Workshopshed/EnchantedObjects/Code/Examples/Blinker/123DDemo.png

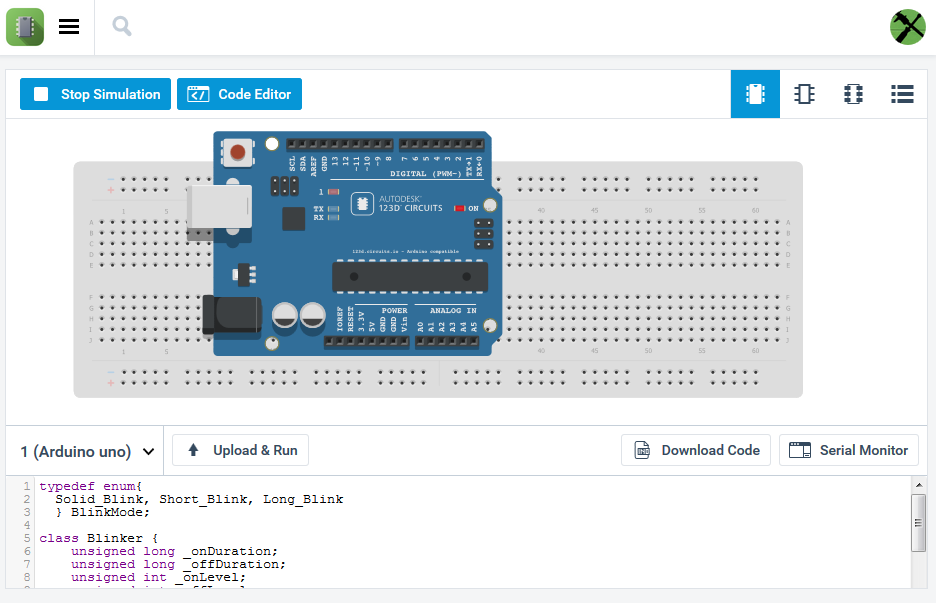
Code/Examples/Blinker/123DDemo.png
