Workshopshed/EnchantedObjects/Code/Examples/HandshakingMonitor/BootOff.jpg

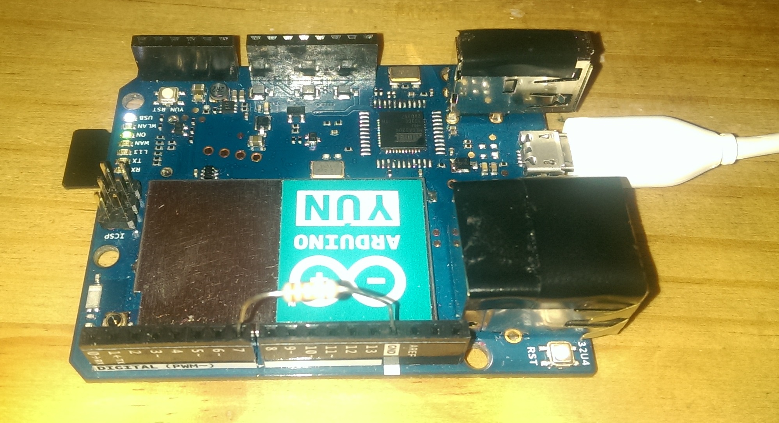
Code/Examples/HandshakingMonitor/BootOff.jpg
