Workshopshed/EnchantedObjects/Code/Examples/HandshakingMonitor/BootOn.jpg

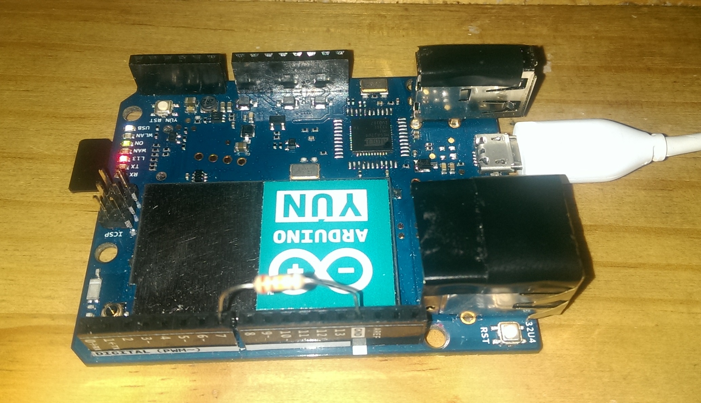
Code/Examples/HandshakingMonitor/BootOn.jpg
