Workshopshed/EnchantedObjects/Code/Examples/HandshakingMonitor/Shell.png

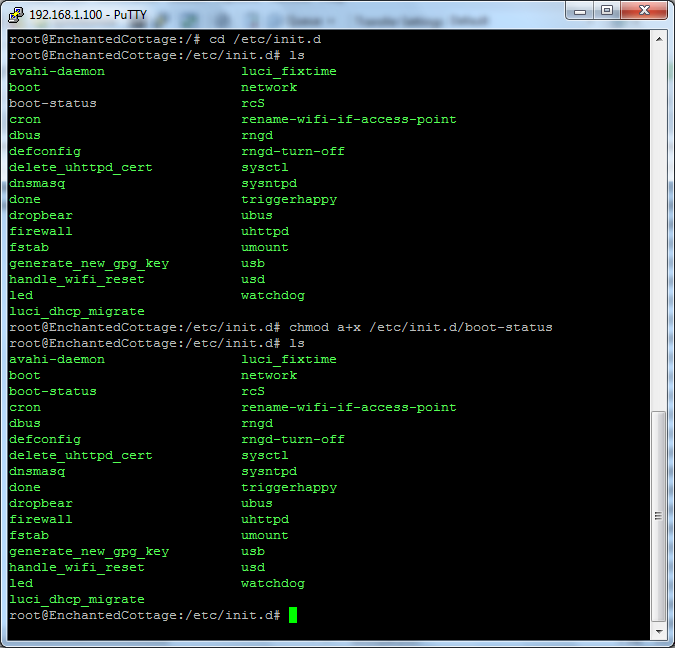
Code/Examples/HandshakingMonitor/Shell.png
