Workshopshed/EnchantedObjects/Code/Examples/LibraryManager.png

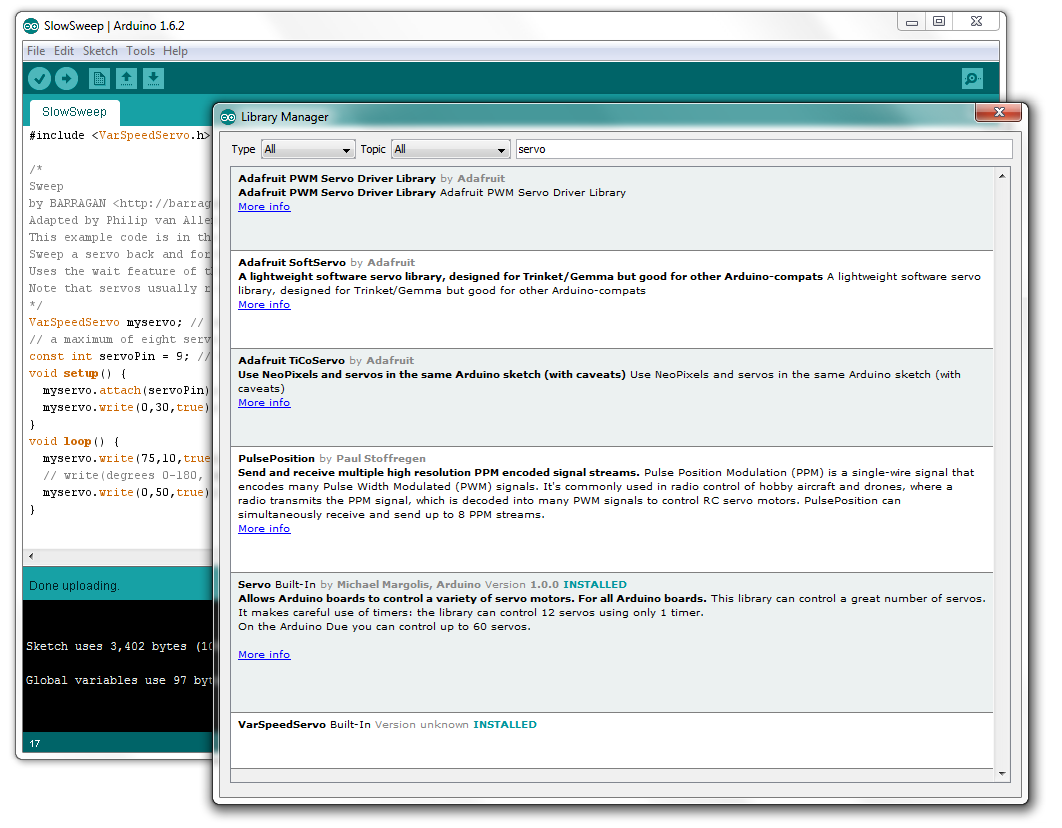
Code/Examples/LibraryManager.png
