Workshopshed/EnchantedObjects/Code/Examples/Python/PythonHello.png

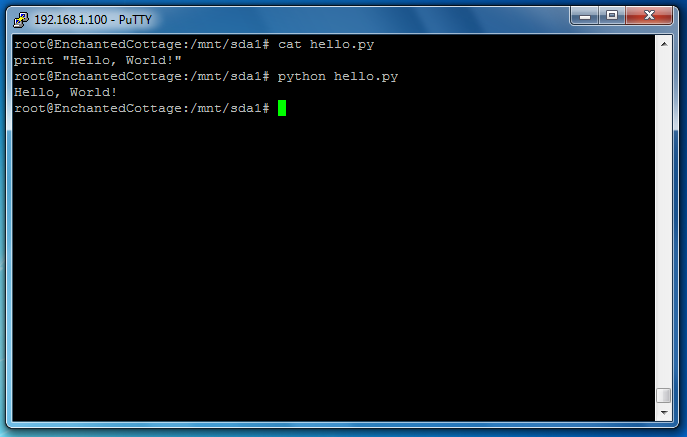
Code/Examples/Python/PythonHello.png
