Workshopshed/EnchantedObjects/Code/Examples/Python/PythonIDE.png

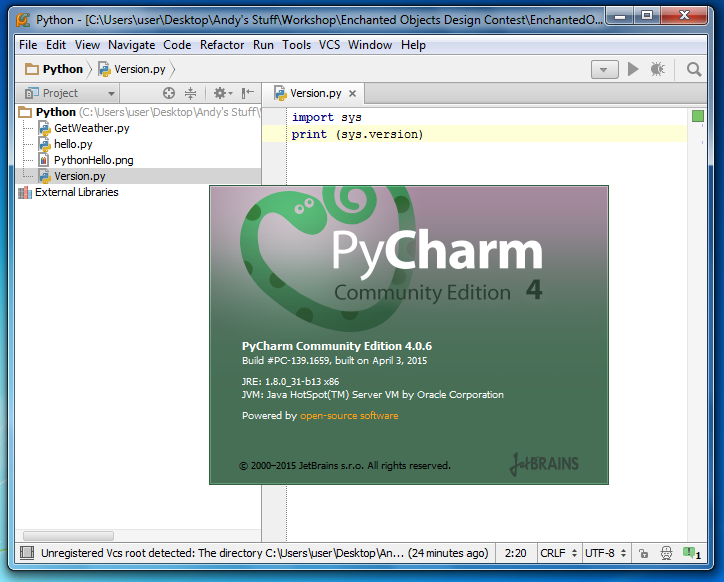
Code/Examples/Python/PythonIDE.png
