Workshopshed/EnchantedObjects/Code/Examples/Python/SourceSync.png

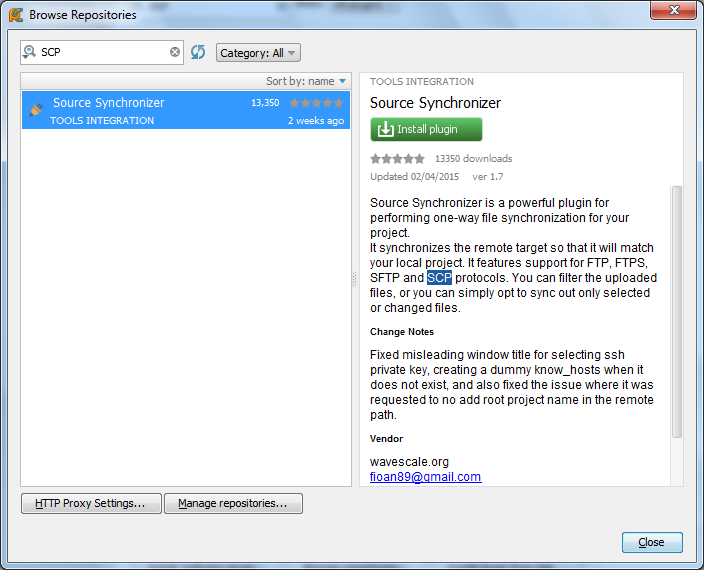
Code/Examples/Python/SourceSync.png
