Workshopshed/EnchantedObjects/Electronics/ComparatorBreadboard.jpg

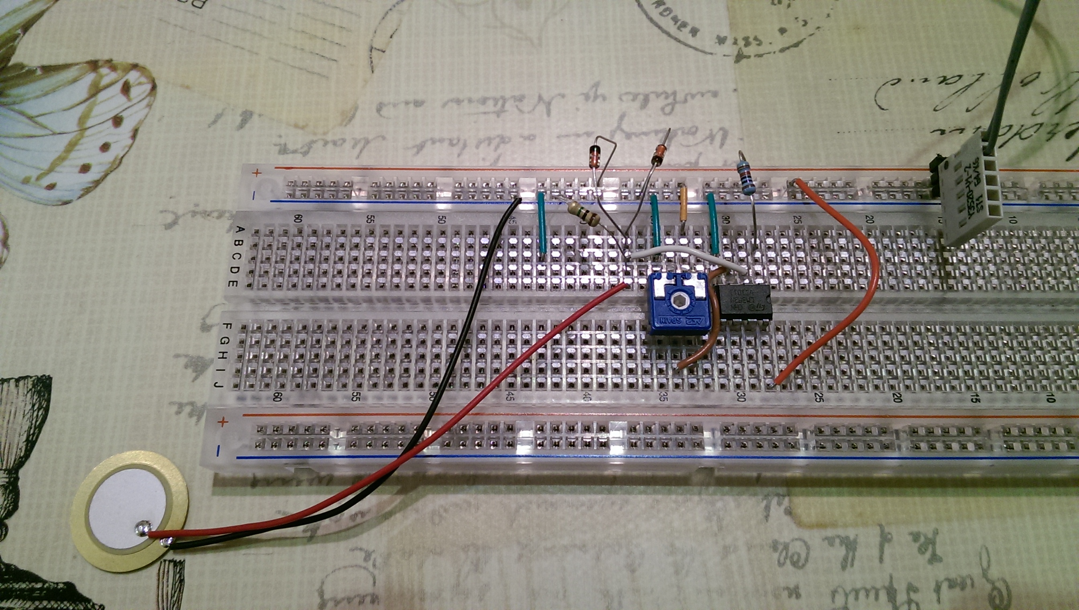
Electronics/ComparatorBreadboard.jpg
