Workshopshed/EnchantedObjects/Electronics/ComparatorStripboard.jpg

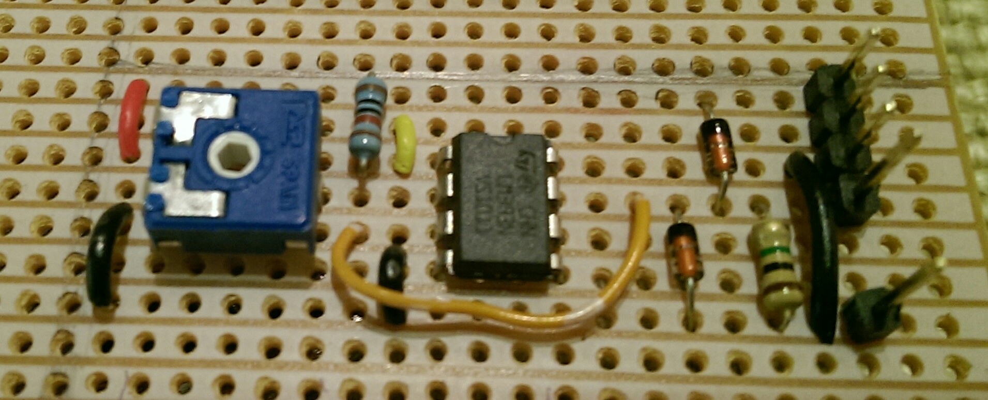
Electronics/ComparatorStripboard.jpg
