Workshopshed/EnchantedObjects/Electronics/DHT22_bb.png

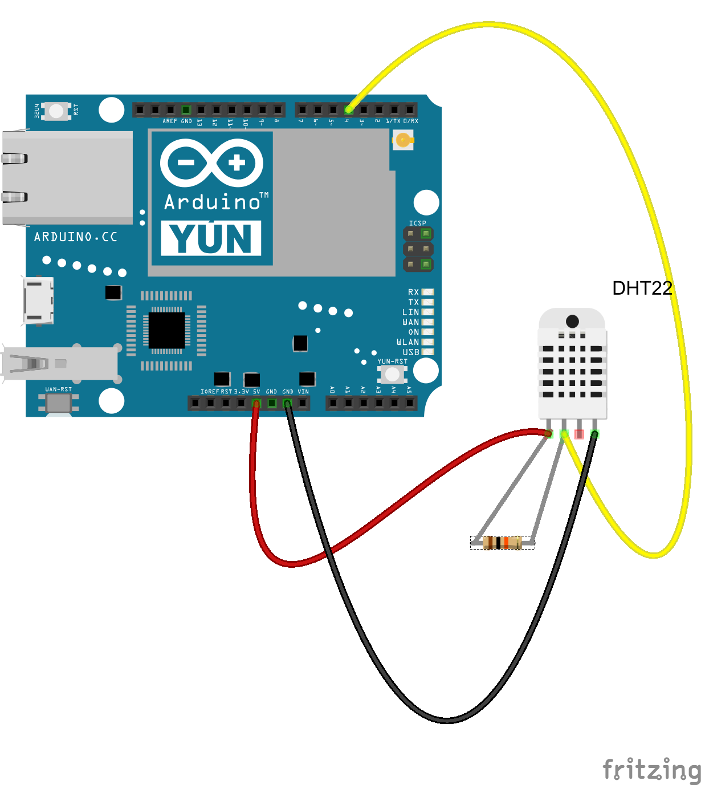
Electronics/DHT22_bb.png
