Workshopshed/EnchantedObjects/Electronics/KnockKnockAndFixedCable.jpg

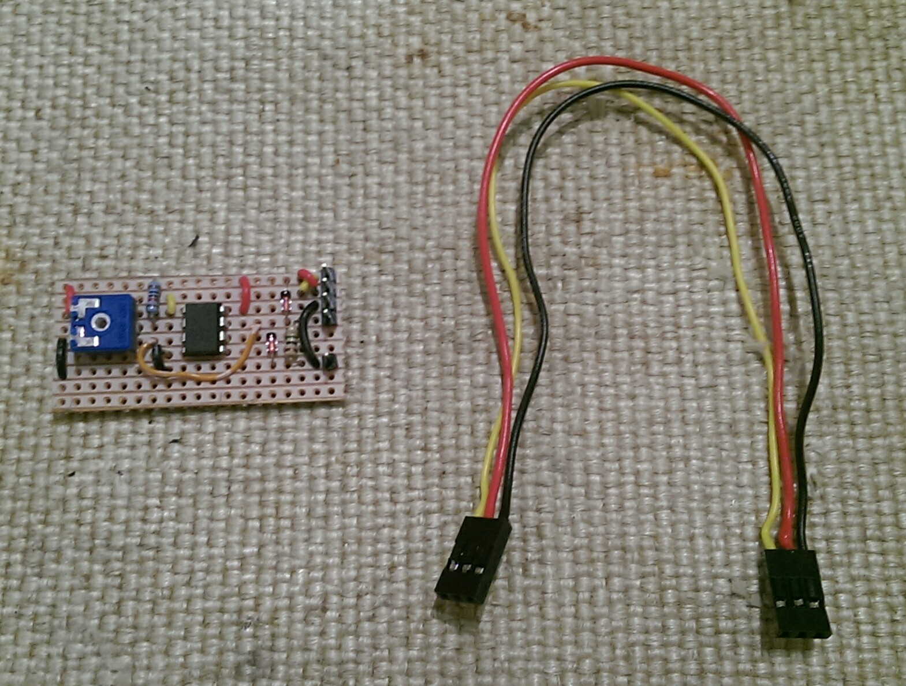
Electronics/KnockKnockAndFixedCable.jpg
