Workshopshed/EnchantedObjects/Electronics/PiezoComparator2b.png

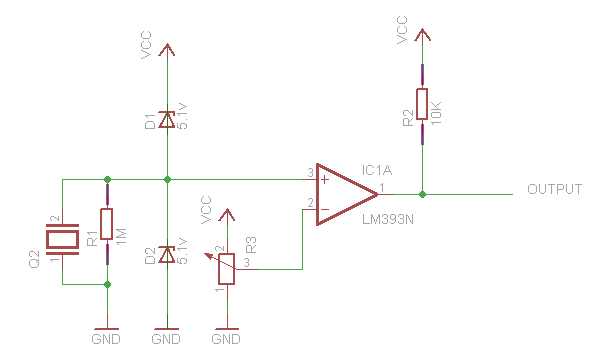
Electronics/PiezoComparator2b.png
