Workshopshed/EnchantedObjects/Electronics/PinsAndBoards.jpg

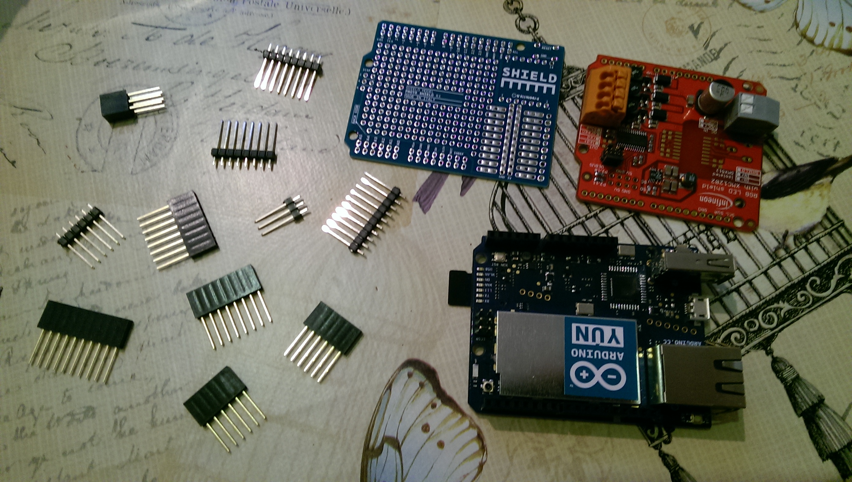
Electronics/PinsAndBoards.jpg
