Workshopshed/EnchantedObjects/Electronics/PowerSwitch.png

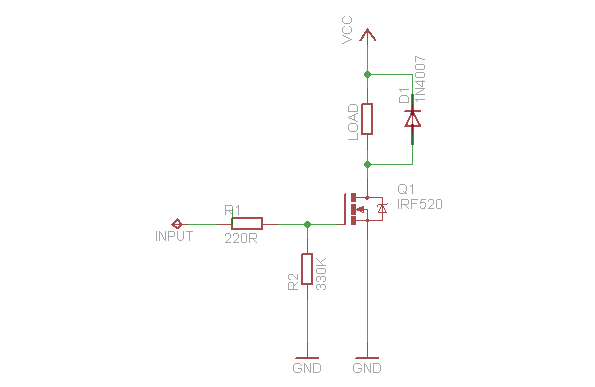
Electronics/PowerSwitch.png
