Workshopshed/EnchantedObjects/Electronics/RGB Demo_schem.png

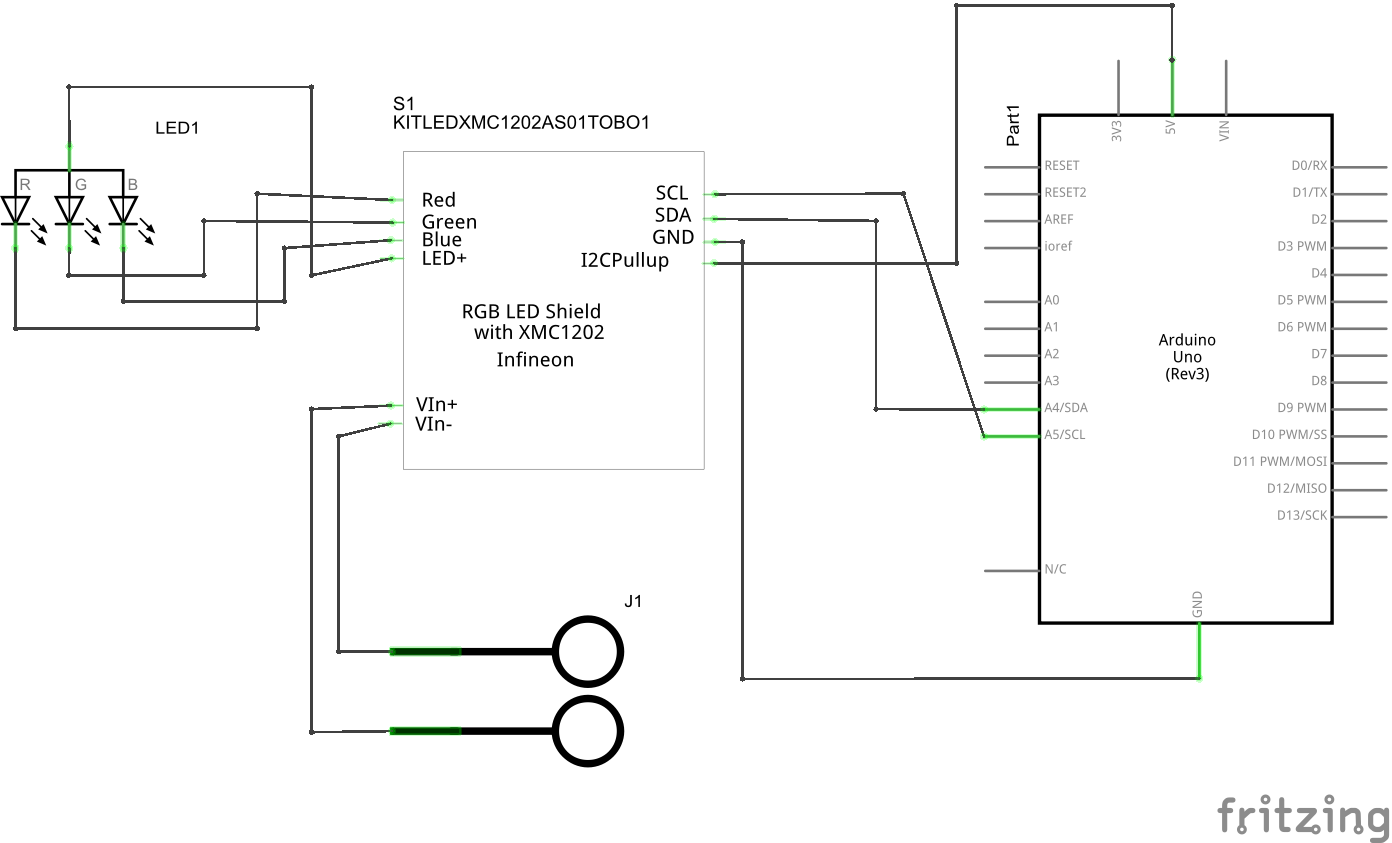
Electronics/RGB Demo_schem.png
