Workshopshed/EnchantedObjects/Electronics/Schematic.png

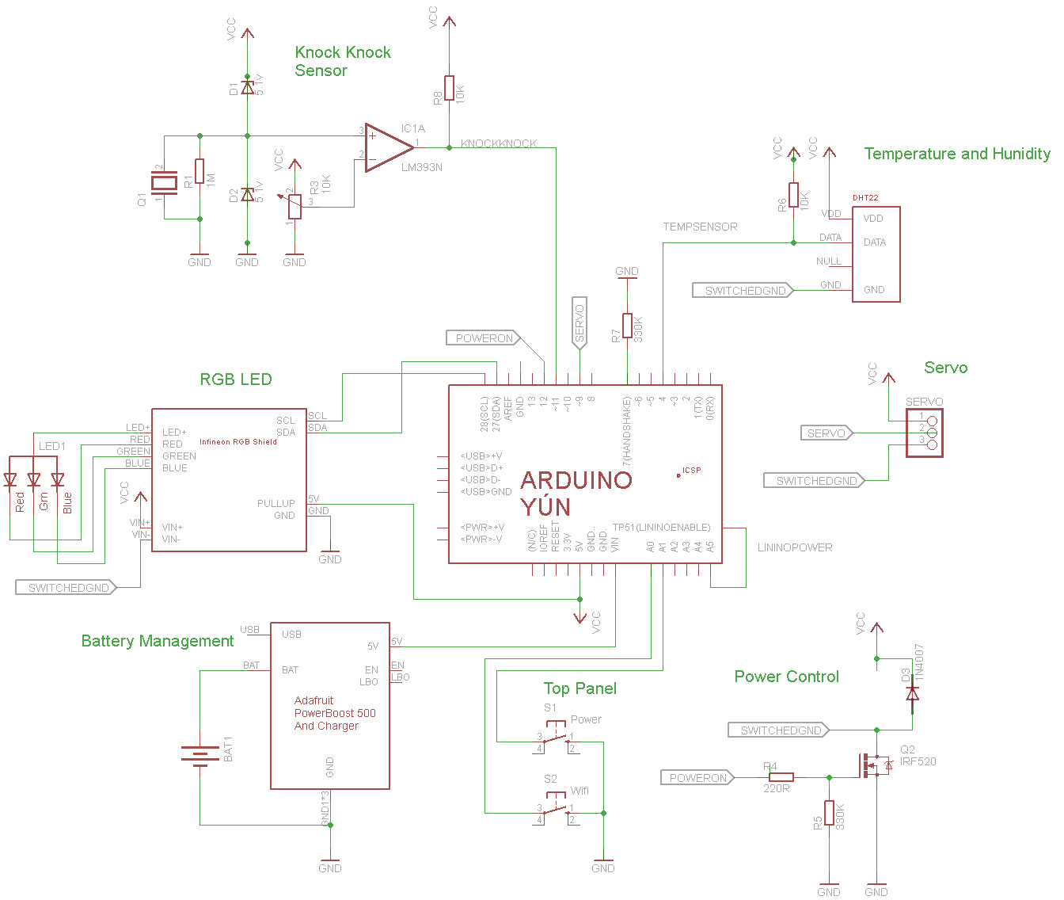
Electronics/Schematic.png
