Workshopshed/EnchantedObjects/Mechanics/FibreHousing.png

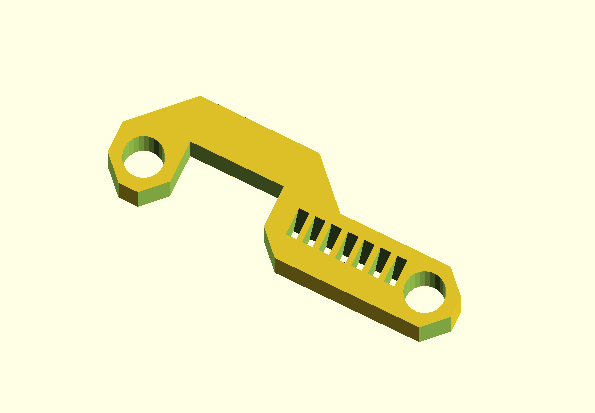
Mechanics/FibreHousing.png
