Workshopshed/EnchantedObjects/Mechanics/MagnetCarriers2.jpg

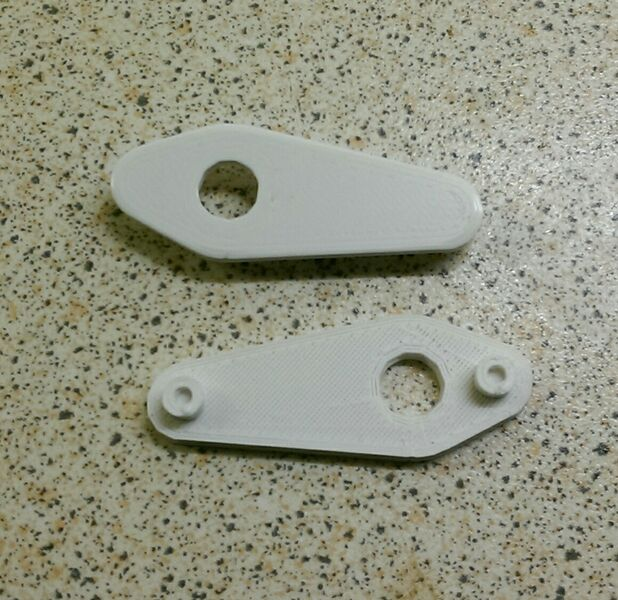
Mechanics/MagnetCarriers2.jpg
