Workshopshed/EnchantedObjects/Mechanics/MagnetCarriers2.png

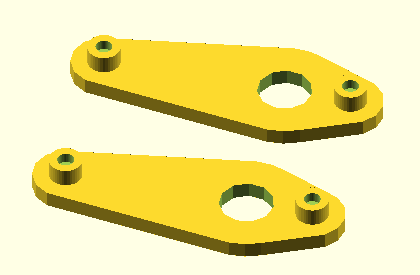
Mechanics/MagnetCarriers2.png
