Workshopshed/EnchantedObjects/Mechanics/Spacers.jpg

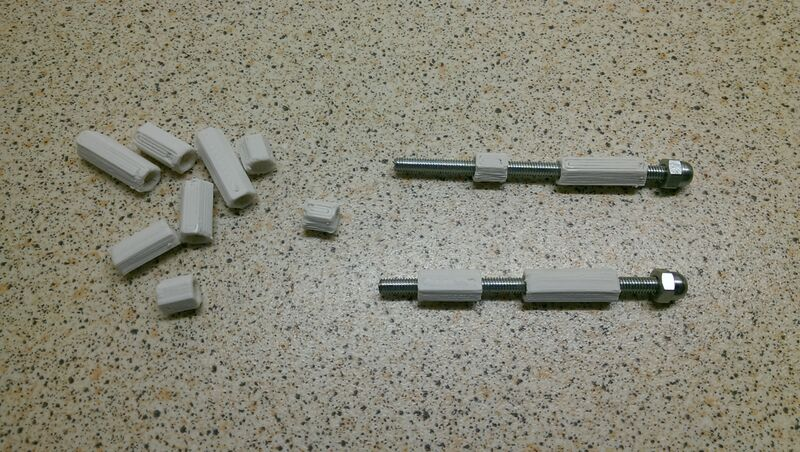
Mechanics/Spacers.jpg
