Workshopshed/EnchantedObjects/Mechanics/Spacers.png

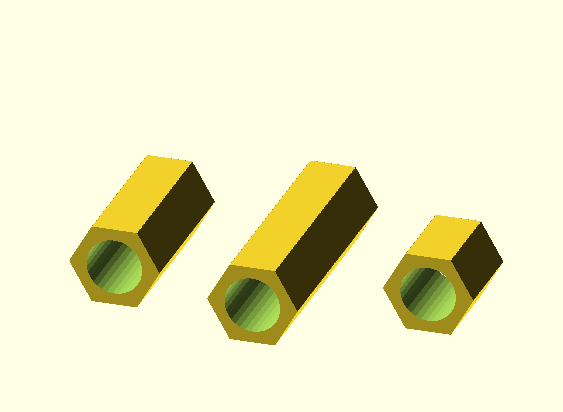
Mechanics/Spacers.png
