Workshopshed/EnchantedObjects/Mechanics/MechanismParts.png

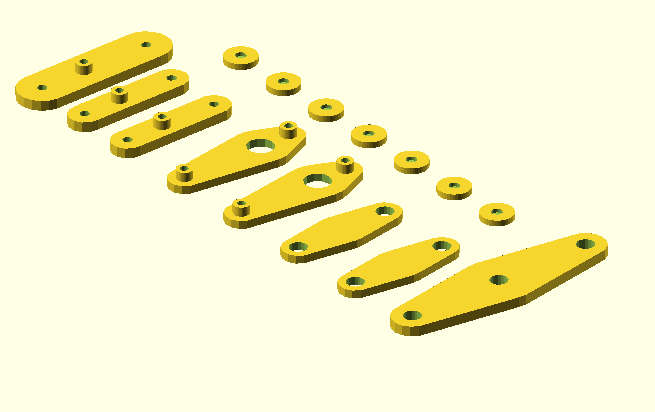
Mechanics/MechanismParts.png
