Workshopshed/EnchantedObjects/Mechanics/WoodParts.png

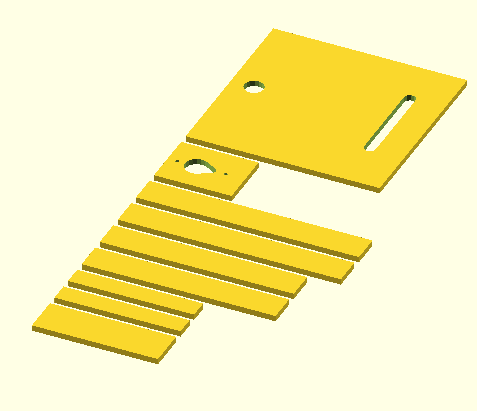
Mechanics/WoodParts.png
