Workshopshed/EnchantedObjects/Electronics/ProtoshieldWiring.jpg

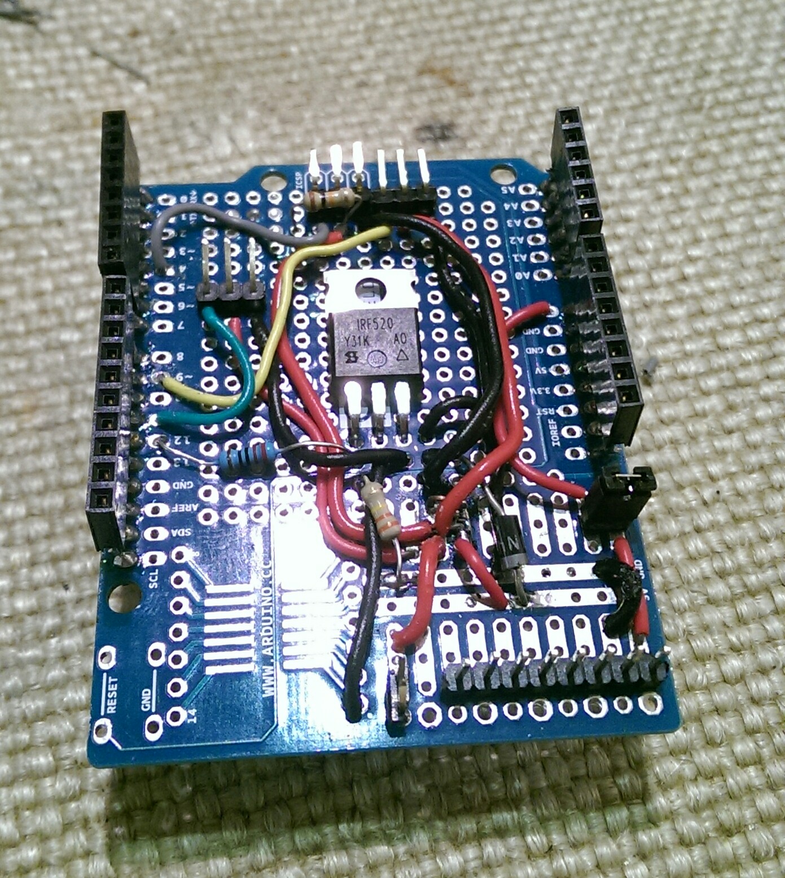
Electronics/ProtoshieldWiring.jpg
