Workshopshed/EnchantedObjects/Electronics/PowerTestBreadboard.jpg

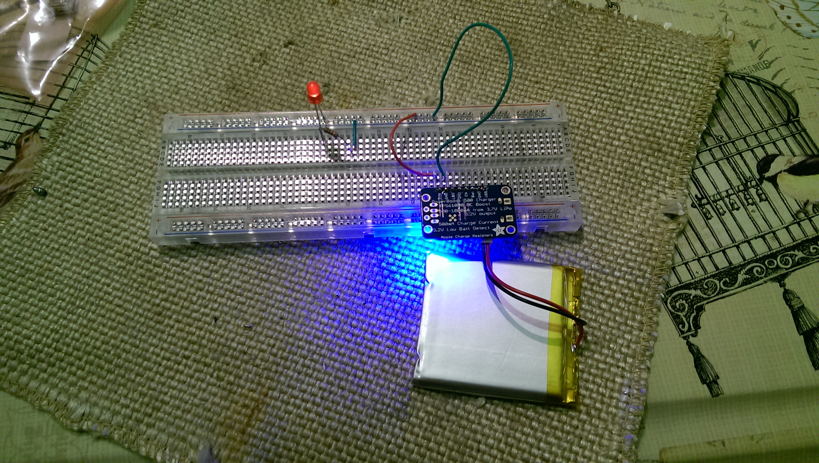
Electronics/PowerTestBreadboard.jpg
