Workshopshed/EnchantedObjects/Electronics/TestFitting.jpg

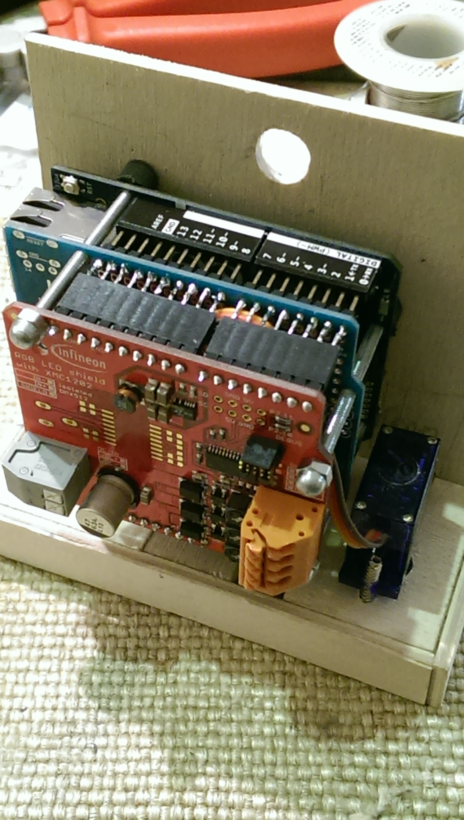
Electronics/TestFitting.jpg
