Workshopshed/EnchantedObjects/Electronics/EnchantedCottage.sch

## EAGLE design Electronics/EnchantedCottage.sch (2015-06-26)

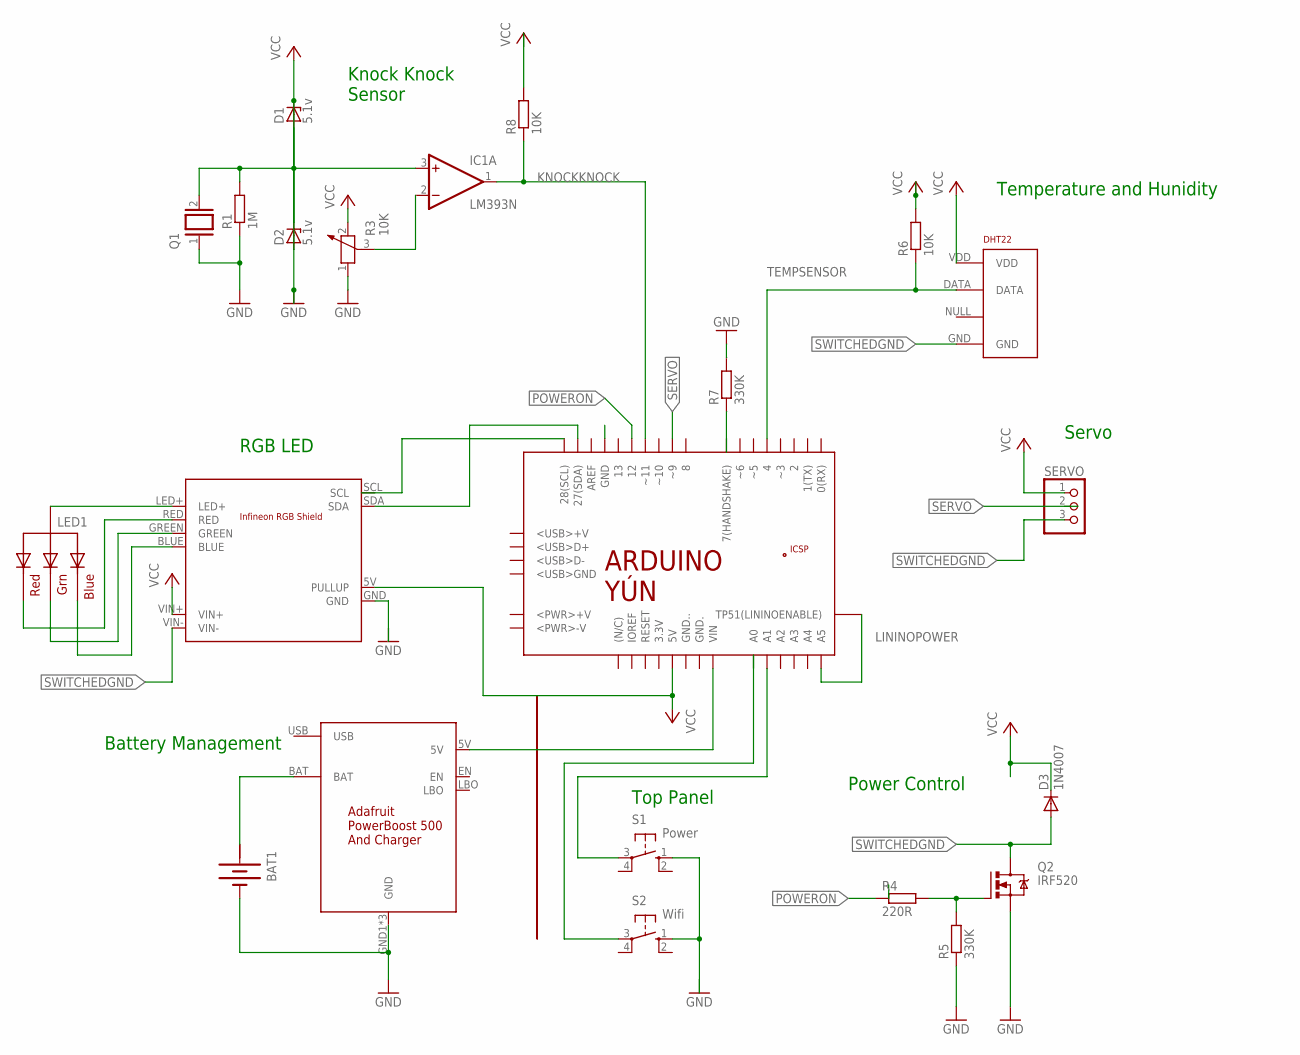
[picture p43: schematic EnchantedCottage.sch]

Parts:
BAT1: BATTERY
D1, D2: 5.1v; DO35Z10
D3: 1N4007; C1702-15
DHT22: RHT03_DHT-22_AM2302; RHT03_DHT-22
IC1: LM393N; DIL08
LED1: RGBLED_CA-5MM; LED5MMRGB
Q1: XTAL/S; QS
Q2: IRF520; TO220BV
R1: 1M; 0204/7
R3: 10K; PT-10
R4: 220R; 0207/12
R5: 330K; 0207/12
R6, R8: 10K; 0204/7
R7: 330K; 0204/7
S1: Power; B3F-10XX
S2: Wifi; B3F-10XX
SERVO: PINHD-1X3; 1X03
U$1: POWERBOOST500; PINS
U$2: RGBSHIELD

Connections:
GND: BAT1.-, Q1.1, Q2.S, R1.1, R3.1, R5.1, R7.2, S1.1 (S), S2.1 (S), U$1.GND1 (GND)
KNOCKKNOCK: IC1.1 (OUT), R8.1
unnamed: IC1.2 (-IN), R3.3
unnamed: D1.A, D2.C, IC1.3 (+IN), Q1.2, R1.2
unnamed: Q2.G, R4.2, R5.2
unnamed: BAT1.+, U$1.BAT
unnamed: LED1.2 (VCC), U$2.LED+
unnamed: LED1.1 (RED), U$2.RED
unnamed: LED1.3 (GREEN), U$2.GREEN
unnamed: LED1.4 (BLUE), U$2.BLUE
POWERON: R4.1
SWITCHEDGND: D3.A, DHT22.GND, Q2.D, SERVO.3
TEMPSENSOR: DHT22.DATA, R6.1
VCC: D1.C, D2.A, D3.C, DHT22.VDD, R3.2, SERVO.1, U$2.5V (PULLUP), U$2.VIN+

Notes on the sheet:
Power Control
Knock Knock Sensor
Servo
Temperature and Hunidity
RGB LED
Battery Management
Top Panel
