Workshopshed/EnchantedObjects/Code/Python/PyCurl.py

import pycurl
from StringIO import StringIO

buffer = StringIO()
c = pycurl.Curl()
c.setopt(c.URL, "https://query.yahooapis.com/v1/public/yql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'c'%3B&format=json&env=store%3A%2F%2Fdatatables.org%2Falltableswithkeys")
c.setopt(c.WRITEDATA, buffer)
c.perform()
c.close()

body = buffer.getvalue()
# Body is a string in some encoding.
# In Python 2, we can print it without knowing what the encoding is.
print(body)
