Workshopshed/EnchantedObjects/Code/Examples/ProcessCurlTest/ProcessCurlTest.ino

#include <Process.h>

void setup() {
  // Initialize Bridge
  Bridge.begin();

  // Initialize Serial
  Serial.begin(9600);

  // Wait until a Serial Monitor is connected.
  while (!Serial);

  // run various example processes
  runCurl();
}

void loop() {
  // Do nothing here.
}

void runCurl() {
  // Launch "curl" command and get Arduino ascii art logo from the network
  // curl is command line program for transferring data using different internet protocols
  Process p;        // Create a process and call it "p"
  p.begin("curl");  // Process that launch the "curl" command
  p.addParameter("http://query.yahooapis.com/v1/public/yql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(select%20woeid%20from%20geo.places(1)%20where%20text%3D%22Chicago%20IL%22)&format=json&env=store%3A%2F%2Fdatatables.org%2Falltableswithkeys"); // Add the URL parameter to "curl"
  p.run();      // Run the process and wait for its termination

  // Print arduino logo over the Serial
  // A process output can be read with the stream methods
  while (p.available()>0) {
    char c = p.read();
    Serial.print(c);
  }
  // Ensure the last bit of data is sent.
  Serial.flush();
}
