Workshopshed/EnchantedObjects/Code/DemoController/Blink.h

#if defined(ARDUINO) && ARDUINO >= 100
#include <Arduino.h>
#else
#include <WProgram.h>
#endif

#if not defined(INFINEONRGB_H)
  typedef enum{
	White, Silver, Gray, Black, Red, Orange, Maroon, Yellow, Olive, Lime, Green, Aqua, Teal, Blue, Navy, Fuchsia, Purple, ColourMax = Purple
	}Colours;
#endif

typedef enum{
  Blink_Off, Blink_Solid, Blink_Short, Blink_Long, Blink_Cycle	
  } BlinkMode;

class Blinker {
    unsigned long _onDuration;
    unsigned long _offDuration;
    unsigned int _onLevel;
    unsigned int _offLevel;
    unsigned long _iTimeout;
    boolean _state;
    uint8_t _colour;
    uint8_t _mode;
  public:
    Blinker(unsigned int onLevel, unsigned int offLevel);
    unsigned long Level(void);
    void Blink(uint8_t Mode);
    void SetColour(uint8_t Colour);  //Uses the colour from infineorgb.h
    uint8_t GetColour(void);    
};
